kihunsong22/JLink-adapter-board/Pics/2.jpg

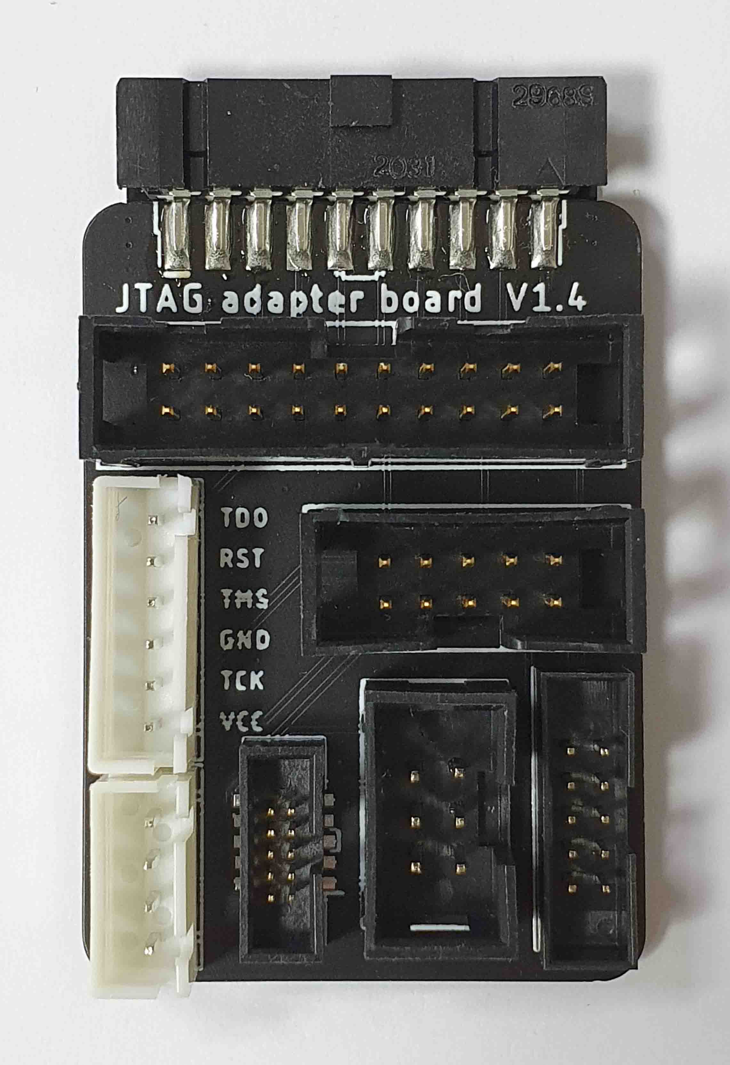
Pics/2.jpg
