kihunsong22/JLink-adapter-board/Pics/3.jpg

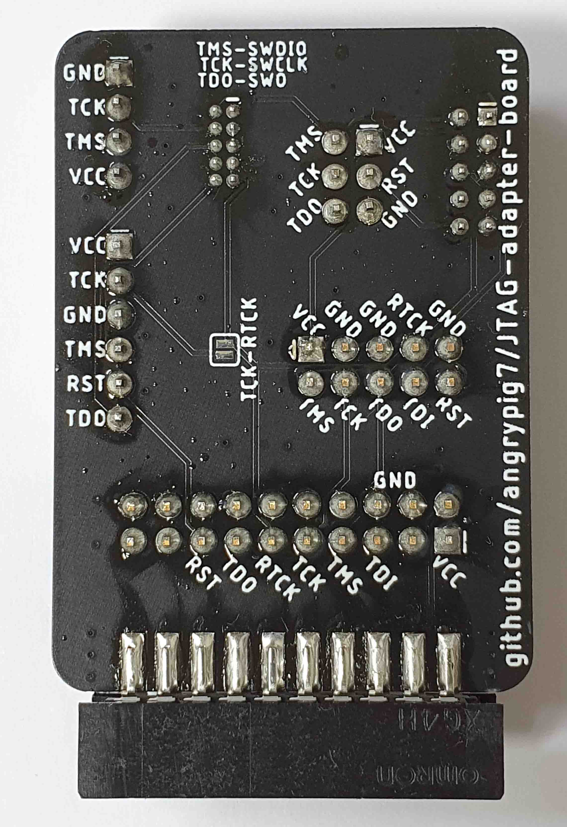
Pics/3.jpg
